sheng00125/LIV_handhold/livox_ros_driver/livox_ros_driver/livox_ros_driver.cpp

//
// The MIT License (MIT)
//
// Copyright (c) 2019 Livox. All rights reserved.
//
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

#include "include/livox_ros_driver.h"

#include <chrono>
#include <vector>
#include <csignal>

#include <ros/ros.h>
#include "lddc.h"
#include "lds_hub.h"
#include "lds_lidar.h"
#include "lds_lvx.h"
#include "livox_sdk.h"
#include <sys/stat.h>
#include <unistd.h>
using namespace livox_ros;

const int32_t kSdkVersionMajorLimit = 2;

inline void SignalHandler(int signum) {
  printf("livox ros driver will exit\r\n");
  ros::shutdown();
  exit(signum);
}

struct time_stamp {
  int64_t high;
  int64_t low;
};
struct time_stamp *pointt;
#define ERR_EXIT(m)                                                            \
  do {                                                                         \
    perror(m);                                                                 \
    exit(EXIT_FAILURE);                                                        \
  } while (0)

int main(int argc, char **argv) {
  /** Ros related */
  if (ros::console::set_logger_level(ROSCONSOLE_DEFAULT_NAME,
                                     ros::console::levels::Debug)) {
    ros::console::notifyLoggerLevelsChanged();
  }
  ros::init(argc, argv, "livox_lidar_publisher");
  ros::NodeHandle livox_node;

  ROS_INFO("Livox Ros Driver Version: %s", LIVOX_ROS_DRIVER_VERSION_STRING);
  signal(SIGINT, SignalHandler);
  /** Check sdk version */
  LivoxSdkVersion _sdkversion;
  GetLivoxSdkVersion(&_sdkversion);
  if (_sdkversion.major < kSdkVersionMajorLimit) {
    ROS_INFO("The SDK version[%d.%d.%d] is too low", _sdkversion.major,
             _sdkversion.minor, _sdkversion.patch);
    return 0;
  }

  /** Init default system parameter */
  int xfer_format = kPointCloud2Msg;
  int multi_topic = 0;
  int data_src = kSourceRawLidar;
  double publish_freq  = 10.0; /* Hz */
  int output_type      = kOutputToRos;
  std::string frame_id = "livox_frame";
  bool lidar_bag = true;
  bool imu_bag   = false;
  livox_node.getParam("xfer_format", xfer_format);
  livox_node.getParam("multi_topic", multi_topic);
  livox_node.getParam("data_src", data_src);
  livox_node.getParam("publish_freq", publish_freq);
  livox_node.getParam("output_data_type", output_type);
  livox_node.getParam("frame_id", frame_id);
  livox_node.getParam("enable_lidar_bag", lidar_bag);
  livox_node.getParam("enable_imu_bag", imu_bag);
  const char *user_name = getlogin();
  std::string path_for_time_stamp = "/home/" + std::string(user_name) + "/timeshare";
  const char *shared_file_name = path_for_time_stamp.c_str();
  int fd = open(shared_file_name, O_CREAT | O_RDWR | O_TRUNC, 0666);
  if (fd == -1) {
    ERR_EXIT("open");
  } else {
    printf("open code: %d\n", fd);
  }
  lseek(fd, sizeof(time_stamp) * 1, SEEK_SET);
  write(fd, "", 1);
  pointt = (time_stamp *)mmap(NULL, sizeof(time_stamp) * 1,
                              PROT_READ | PROT_WRITE, MAP_SHARED, fd, 0);

  if (publish_freq > 100.0) {
    publish_freq = 100.0;
  } else if (publish_freq < 0.1) {
    publish_freq = 0.1;
  } else {
    publish_freq = publish_freq;
  }

  /** Lidar data distribute control and lidar data source set */
  Lddc *lddc = new Lddc(xfer_format, multi_topic, data_src, output_type,
                        publish_freq, frame_id, lidar_bag, imu_bag);
  lddc->SetRosNode(&livox_node);

  int ret = 0;
  if (data_src == kSourceRawLidar) {
    ROS_INFO("Data Source is raw lidar.");

    std::string user_config_path;
    livox_node.getParam("user_config_path", user_config_path);
    ROS_INFO("Config file : %s", user_config_path.c_str());

    std::string cmdline_bd_code;
    livox_node.getParam("cmdline_str", cmdline_bd_code);

    std::vector<std::string> bd_code_list;
    ParseCommandlineInputBdCode(cmdline_bd_code.c_str(), bd_code_list);

    LdsLidar *read_lidar = LdsLidar::GetInstance(1000 / publish_freq);
    lddc->RegisterLds(static_cast<Lds *>(read_lidar));
    // 里面有回调函数
    ret = read_lidar->InitLdsLidar(bd_code_list, user_config_path.c_str());
    if (!ret) {
      ROS_INFO("Init lds lidar success!");
    } else {
      ROS_ERROR("Init lds lidar fail!");
    }
  } else if (data_src == kSourceRawHub) {
    ROS_INFO("Data Source is hub.");

    std::string user_config_path;
    livox_node.getParam("user_config_path", user_config_path);
    ROS_INFO("Config file : %s", user_config_path.c_str());

    std::string cmdline_bd_code;
    livox_node.getParam("cmdline_str", cmdline_bd_code);

    std::vector<std::string> bd_code_list;
    ParseCommandlineInputBdCode(cmdline_bd_code.c_str(), bd_code_list);

    LdsHub *read_hub = LdsHub::GetInstance(1000 / publish_freq);
    lddc->RegisterLds(static_cast<Lds *>(read_hub));
    ret = read_hub->InitLdsHub(bd_code_list, user_config_path.c_str());
    if (!ret) {
      ROS_INFO("Init lds hub success!");
    } else {
      ROS_ERROR("Init lds hub fail!");
    }
  } else {
    ROS_INFO("Data Source is lvx file.");

    std::string cmdline_file_path;
    livox_node.getParam("cmdline_file_path", cmdline_file_path);

    do {
      if (!IsFilePathValid(cmdline_file_path.c_str())) {
        ROS_ERROR("File path invalid : %s !", cmdline_file_path.c_str());
        break;
      }

      std::string rosbag_file_path;
      int path_end_pos = cmdline_file_path.find_last_of('.');
      rosbag_file_path = cmdline_file_path.substr(0, path_end_pos);
      rosbag_file_path += ".bag";

      LdsLvx *read_lvx = LdsLvx::GetInstance(1000 / publish_freq);
      lddc->RegisterLds(static_cast<Lds *>(read_lvx));
      lddc->CreateBagFile(rosbag_file_path);
      int ret = read_lvx->InitLdsLvx(cmdline_file_path.c_str());
      if (!ret) {
        ROS_INFO("Init lds lvx file success!");
      } else {
        ROS_ERROR("Init lds lvx file fail!");
      }
    } while (0);
  }

  ros::Time::init();
  while (ros::ok()) {
    lddc->DistributeLidarData();
  }
  munmap(pointt, sizeof(time_stamp) * 5);
  return 0;
}
