sheng00125/LIV_handhold/stm32_timersync-open/HARDWARE/TIMER/timer.c

#include "timer.h"
#include "led.h"
#include "usart.h"
#include "sys.h"
#include <stdio.h>
#include <string.h>

//1,增加TIM3_PWM_Init函数。
//2,增加LED0_PWM_VAL宏定义，控制TIM3_CH2脉宽									  
//////////////////////////////////////////////////////////////////////////////////  
   	  
//通用定时器3中断初始化
//这里时钟选择为APB1的2倍，而APB1为36M
//arr：自动重装值。
//psc：时钟预分频数
//这里使用的是定时器3!
void TIM3_Int_Init(u16 arr,u16 psc)
{
  TIM_TimeBaseInitTypeDef  TIM_TimeBaseStructure;
	NVIC_InitTypeDef NVIC_InitStructure;

	RCC_APB1PeriphClockCmd(RCC_APB1Periph_TIM3, ENABLE); //时钟使能

	TIM_TimeBaseStructure.TIM_Period = arr; //设置在下一个更新事件装入活动的自动重装载寄存器周期的值	 计数到5000为500ms
	TIM_TimeBaseStructure.TIM_Prescaler =psc; //设置用来作为TIMx时钟频率除数的预分频值  10Khz的计数频率  
	TIM_TimeBaseStructure.TIM_ClockDivision = 0; //设置时钟分割:TDTS = Tck_tim
	TIM_TimeBaseStructure.TIM_CounterMode = TIM_CounterMode_Up;  //TIM向上计数模式
	TIM_TimeBaseInit(TIM3, &TIM_TimeBaseStructure); //根据TIM_TimeBaseInitStruct中指定的参数初始化TIMx的时间基数单位
 
	TIM_ITConfig(TIM3,TIM_IT_Update,ENABLE ); //使能指定的TIM3中断,允许更新中断

	NVIC_InitStructure.NVIC_IRQChannel = TIM3_IRQn;  //TIM3中断
	NVIC_InitStructure.NVIC_IRQChannelPreemptionPriority = 0;  //先占优先级0级
	NVIC_InitStructure.NVIC_IRQChannelSubPriority = 3;  //从优先级3级
	NVIC_InitStructure.NVIC_IRQChannelCmd = ENABLE; //IRQ通道被使能
	NVIC_Init(&NVIC_InitStructure);  //根据NVIC_InitStruct中指定的参数初始化外设NVIC寄存器

	TIM_Cmd(TIM3, ENABLE);  //使能TIMx外设
							 
}




vu16 varl=0;
//定时器3中断服务程序
vu16 var_Exp=0;
vu16 global_time;
char snum[7];
vu16 shorttt=0;

char gprmcStr[7]="$GPRMC,";
int chckNum=0;
char chckNumChar[2];

int ss=0;
int mm=0;
int hh=0;

unsigned char result;
int i;
int checkNum(const char *gprmcContext)
{
    if (gprmcContext == NULL) 
    {
        // printf("Input is NULL.\n");
        return -1;
		}

    result = gprmcContext[1];

    for (i = 2; gprmcContext[i] != '*' && gprmcContext[i] != '\0'; i++)
    {
        // printf("Processing character: %c (ASCII: %d)\n", gprmcContext[i], gprmcContext[i]);
        result ^= gprmcContext[i];
    }

    if (gprmcContext[i] != '*') 
    {
        // printf("No '*' found in the string.\n");
        return -1;
    }

    //printf("Final result before returning: %02X\n", result);
    return result;
}

char value_1[100]="";
char value_2[100]="";
char value_time[10]="";

char test[100]="$GPRMC,004015,A,2812.0498,N,11313.1361,E,0.0,180.0,150122,3.9,W,A*";
void TIM3_IRQHandler(void)   //TIM3中断
{


		if (TIM_GetITStatus(TIM3, TIM_IT_Update) != RESET) //检查指定的TIM中断发生与否:TIM 中断源 
		{
		TIM_ClearITPendingBit(TIM3, TIM_IT_Update  );  //清除TIMx的中断待处理位:TIM 中断源 
		LED1=!LED1;
			
			//var_Exp 做半曝光时长的相移操作
		TIM2->CNT=TIM2->ARR/2;

		PCout(13)=0;
		}
		
		
		//global_time++;
		//shorttt=0;
		//sprintf(snum, "%06d", global_time); //产生："000011D7"
		//snum[6]=0;
		//printf("$GPRMC,");
	  //printf(snum);
		//printf(".00,A,2237.496474,N,11356.089515,E,0.0,225.5,310518,2.3,W,A*23\n");
		

		
		//************************************* add *********************************************
		//UTCtime format: hhmmss
		
    if(ss<59){
				ss++;
		}else{
			  ss=0;
			 if(mm<59){
				 mm++;
			 }else{
				 mm=0;
				 if(hh<23){
					 hh++;
				 }else{
					 hh=0;
				 }
			 }
		}
		
    sprintf(value_2, "%s%02d%02d%02d%s", gprmcStr, hh, mm, ss, ".00,A,2237.496474,N,11356.089515,E,0.0,225.5,230520,2.3,W,A*");
		strcpy(value_1,value_2);
	  chckNum =checkNum(value_1);
	  sprintf(chckNumChar, "%02X", chckNum);
		printf("%s", value_2);
    printf("%s\n", chckNumChar);
	 
		
	  //**********************************************************************************

		/**
		chckNum=checkNum(test);	
	  sprintf(chckNumChar, "%02X", chckNum);
    printf("%s\n", chckNumChar);
    */
}



void TIM2_PWM_Init(u16 arr,u16 psc)
{  
	GPIO_InitTypeDef GPIO_InitStructure;
  TIM_TimeBaseInitTypeDef TIM_TimeBaseStructure;
  TIM_OCInitTypeDef TIM_OCInitStructure;
	

	RCC_APB1PeriphClockCmd(RCC_APB1Periph_TIM2, ENABLE); 
  RCC_APB2PeriphClockCmd(RCC_APB2Periph_GPIOA, ENABLE); 
	TIM_DeInit(TIM2);
 
 
	GPIO_InitStructure.GPIO_Pin = GPIO_Pin_1; //TIM_CH1  B6 pin out
	GPIO_InitStructure.GPIO_Mode = GPIO_Mode_AF_PP;  //??????
	GPIO_InitStructure.GPIO_Speed = GPIO_Speed_50MHz;
	GPIO_Init(GPIOA, &GPIO_InitStructure);//???GPIO
 
   //???TIM4
	TIM_TimeBaseStructure.TIM_Period = arr; 
	TIM_TimeBaseStructure.TIM_Prescaler =psc; 
	TIM_TimeBaseStructure.TIM_ClockDivision = 0; 
	TIM_TimeBaseStructure.TIM_CounterMode = TIM_CounterMode_Up;  
	TIM_TimeBaseInit(TIM2, &TIM_TimeBaseStructure); 
	
	//???TIM4 Channel1 PWM??	 
	TIM_OCInitStructure.TIM_Pulse = 50; //????????????????
	TIM_OCInitStructure.TIM_OCMode = TIM_OCMode_PWM2; //???????:TIM????????2
 	TIM_OCInitStructure.TIM_OutputState = TIM_OutputState_Enable; //??????
	TIM_OCInitStructure.TIM_OCPolarity = TIM_OCPolarity_High; //????:TIM???????
	TIM_OCInitStructure.TIM_OutputNState = TIM_OutputNState_Disable;
	TIM_OC2PreloadConfig(TIM2, TIM_OCPreload_Enable);  //??TIM4?CCR2????????
	TIM_OC2Init(TIM2, &TIM_OCInitStructure);  //??T??????????TIM4 OC2
	
	//???TIM4 Channel2 PWM??	 
//	TIM_OCInitStructure.TIM_Pulse = 500; //????????????????
//	TIM_OCInitStructure.TIM_OCMode = TIM_OCMode_PWM2; //???????:TIM????????2
// 	TIM_OCInitStructure.TIM_OutputState = TIM_OutputState_Enable; //??????
//	TIM_OCInitStructure.TIM_OCPolarity = TIM_OCPolarity_High; //????:TIM???????
//	//TIM_OCInitStructure.TIM_OutputNState = TIM_OutputNState_Disable;
//	TIM_OC2PreloadConfig(TIM4, TIM_OCPreload_Enable);  //??TIM4?CCR2????????
//	TIM_OC2Init(TIM4, &TIM_OCInitStructure);  //??T??????????TIM4 OC2

 	TIM_ARRPreloadConfig(TIM2, ENABLE);
	TIM_Cmd(TIM2, ENABLE);  //??TIM4
	


 //	TIM_SetCompare2(TIM2,50);	 // ccr  set pwm value
TIM_SetCompare2(TIM2,TIM2->ARR/2);
}



//TIM3 PWM部分初始化 
//PWM输出初始化
//arr：自动重装值
//psc：时钟预分频数

//
void TIM3_PWM_Init(u16 arr,u16 psc)
{  
	GPIO_InitTypeDef GPIO_InitStructure;
	TIM_TimeBaseInitTypeDef  TIM_TimeBaseStructure;
	TIM_OCInitTypeDef  TIM_OCInitStructure;
		NVIC_InitTypeDef NVIC_InitStructure;	

	RCC_APB1PeriphClockCmd(RCC_APB1Periph_TIM3, ENABLE);	//使能定时器3时钟
 	RCC_APB2PeriphClockCmd(RCC_APB2Periph_GPIOB  | RCC_APB2Periph_AFIO, ENABLE);  //使能GPIO外设和AFIO复用功能模块时钟
	
	GPIO_PinRemapConfig(GPIO_PartialRemap_TIM3, ENABLE); //Timer3部分重映射  TIM3_CH2->PB5    
 
   //设置该引脚为复用输出功能,输出TIM3 CH2的PWM脉冲波形	GPIOB.5
	GPIO_InitStructure.GPIO_Pin = GPIO_Pin_5; //TIM_CH2
	GPIO_InitStructure.GPIO_Mode = GPIO_Mode_AF_PP;  //复用推挽输出
	GPIO_InitStructure.GPIO_Speed = GPIO_Speed_50MHz;
	GPIO_Init(GPIOB, &GPIO_InitStructure);//初始化GPIO
 
   //初始化TIM3
	TIM_TimeBaseStructure.TIM_Period = arr; //设置在下一个更新事件装入活动的自动重装载寄存器周期的值
	TIM_TimeBaseStructure.TIM_Prescaler =psc; //设置用来作为TIMx时钟频率除数的预分频值 
	TIM_TimeBaseStructure.TIM_ClockDivision = 0; //设置时钟分割:TDTS = Tck_tim
	TIM_TimeBaseStructure.TIM_CounterMode = TIM_CounterMode_Up;  //TIM向上计数模式
	TIM_TimeBaseInit(TIM3, &TIM_TimeBaseStructure); //根据TIM_TimeBaseInitStruct中指定的参数初始化TIMx的时间基数单位
	
	//初始化TIM3 Channel2 PWM模式	 
	TIM_OCInitStructure.TIM_OCMode = TIM_OCMode_PWM2; //选择定时器模式:TIM脉冲宽度调制模式2
 	TIM_OCInitStructure.TIM_OutputState = TIM_OutputState_Enable; //比较输出使能
	TIM_OCInitStructure.TIM_OCPolarity = TIM_OCPolarity_High; //输出极性:TIM输出比较极性高
	TIM_OC2Init(TIM3, &TIM_OCInitStructure);  //根据T指定的参数初始化外设TIM3 OC2

	TIM_OC2PreloadConfig(TIM3, TIM_OCPreload_Enable);  //使能TIM3在CCR2上的预装载寄存器
 
	TIM_Cmd(TIM3, ENABLE);  //使能TIM3
	
	TIM_SetCompare2(TIM3,TIM3->ARR/2);	

	TIM_ITConfig(TIM3,TIM_IT_Update,ENABLE ); //使能指定的TIM3中断,允许更新中断

	NVIC_InitStructure.NVIC_IRQChannel = TIM3_IRQn;  //TIM3中断
	NVIC_InitStructure.NVIC_IRQChannelPreemptionPriority = 0;  //先占优先级0级
	NVIC_InitStructure.NVIC_IRQChannelSubPriority = 3;  //从优先级3级
	NVIC_InitStructure.NVIC_IRQChannelCmd = ENABLE; //IRQ通道被使能
	NVIC_Init(&NVIC_InitStructure);  //根据NVIC_InitStruct中指定的参数初始化外设NVIC寄存器
}
