sheng00125/LIV_handhold/livox_ros_driver/timesync/timesync.cpp

//
// The MIT License (MIT)
//
// Copyright (c) 2019 Livox. All rights reserved.
//
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

#include "timesync.h"

#include <stdint.h>
#include <string.h>
#include <chrono>
#include <cstdio>
#include <functional>
#include <thread>
#include <stdio.h>
namespace livox_ros {
using namespace std;

TimeSync::TimeSync()
    : exit_poll_state_(false),
      start_poll_state_(false),
      exit_poll_data_(false),
      start_poll_data_(false) {
  fsm_state_ = kOpenDev;
  uart_ = nullptr;
  comm_ = nullptr;
  fn_cb_ = nullptr;
  client_data_ = nullptr;
  rx_bytes_ = 0;
}

TimeSync::~TimeSync() { DeInitTimeSync(); }

int32_t TimeSync::InitTimeSync(const TimeSyncConfig &config) {
  config_ = config;

  if (config_.dev_config.type == kCommDevUart) {
    uint8_t baudrate_index = config_.dev_config.config.uart.baudrate;
    uint8_t parity_index = config_.dev_config.config.uart.parity;

    if ((baudrate_index < BRUnkown) && (parity_index < ParityUnkown)) {
      uart_ = new UserUart(baudrate_index, parity_index);
    } else {
      printf("Uart parameter error, please check the configuration file!\n");
      return -1;
    }
  } else {
    printf("Device type not supported, now only uart is supported!\n");
    return -1;
  }

  config_.protocol_config.type = kGps;
  comm_ = new CommProtocol(config_.protocol_config);

  t_poll_state_ =
      std::make_shared<std::thread>(std::bind(&TimeSync::PollStateLoop, this));
  t_poll_data_ =
      std::make_shared<std::thread>(std::bind(&TimeSync::PollDataLoop, this));

  return 0;
}

int32_t TimeSync::DeInitTimeSync() {
  StopTimesync();

  if (uart_) delete uart_;
  if (comm_) delete comm_;

  fn_cb_ = nullptr;
  client_data_ = nullptr;
  return 0;
}

void TimeSync::StopTimesync() {
  start_poll_state_ = false;
  start_poll_data_ = false;
  exit_poll_state_ = true;
  exit_poll_data_ = true;
  if (t_poll_state_) {
    t_poll_state_->join();
    t_poll_state_ = nullptr;
  }

  if (t_poll_data_) {
    t_poll_data_->join();
    t_poll_data_ = nullptr;
  }
}

void TimeSync::PollStateLoop() {
  while (!start_poll_state_) {
    /* waiting to start */
  }

  while (!exit_poll_state_) {
    if (fsm_state_ == kOpenDev) {
      FsmOpenDev();
    } else if (fsm_state_ == kPrepareDev) {
      FsmPrepareDev();
    } else if (fsm_state_ == kCheckDevState) {
      FsmCheckDevState();
    }
    std::this_thread::sleep_for(std::chrono::milliseconds(50));
  }
}

void TimeSync::PollDataLoop() {
  while (!start_poll_data_) {
    /* waiting to start */
  }

  while (!exit_poll_data_) {
    if (uart_->IsOpen()) {
      uint32_t get_buf_size;
      uint8_t *cache_buf = comm_->FetchCacheFreeSpace(&get_buf_size);
      if (get_buf_size) {
        uint32_t read_data_size;
        read_data_size = uart_->Read((char *)cache_buf, get_buf_size);
        if (read_data_size) {
          comm_->UpdateCacheWrIdx(read_data_size);
          rx_bytes_ += read_data_size;
          CommPacket packet;
          memset(&packet, 0, sizeof(packet));
          // 解析 $GPRMC
          while ((kParseSuccess == comm_->ParseCommStream(&packet))) {
            if (((fn_cb_ != nullptr) || (client_data_ != nullptr))) {
              if ((strstr((const char *)packet.data, "$GPRMC")) ||
                      (strstr((const char *)packet.data , "$GNRMC"))){
                // 这里把包的结果打印出来了
                printf("Received RMC data packet: %s\n", (const char *)packet.data);
                fn_cb_((const char *)packet.data,
                       packet.data_len, client_data_);
                // printf((const char *)client_data_);
                printf("RMC data parse success!.\n");
              }
            }
          }
        }
      }
    } else {
      std::this_thread::sleep_for(std::chrono::milliseconds(50));
    }
  }
}

void TimeSync::FsmTransferState(uint8_t new_state) {
  if (new_state < kFsmDevUndef) {
    fsm_state_ = new_state;
  }
  transfer_time_ = chrono::steady_clock::now();
}

void TimeSync::FsmOpenDev() {
  if (!uart_->IsOpen()) {
    if (!uart_->Open(config_.dev_config.name)) {
      FsmTransferState(kPrepareDev);
    }
  } else {
    FsmTransferState(kPrepareDev);
  }
}

void TimeSync::FsmPrepareDev() {
  chrono::steady_clock::time_point t = chrono::steady_clock::now();
  chrono::milliseconds time_gap =
      chrono::duration_cast<chrono::milliseconds>(t - transfer_time_);
  /** delay some time when device is opened, 4s */
  if (time_gap.count() > 3000) {
    FsmTransferState(kCheckDevState);
  }
}

void TimeSync::FsmCheckDevState() {
  static uint32_t last_rx_bytes = 0;
  static chrono::steady_clock::time_point t1 = chrono::steady_clock::now();

  chrono::steady_clock::time_point t2 = chrono::steady_clock::now();
  chrono::milliseconds time_gap =
      chrono::duration_cast<chrono::milliseconds>(t2 - t1);

  if (time_gap.count() > 2000000) { /* period : 2.5s */
    if (last_rx_bytes == rx_bytes_) {
      uart_->Close();
      FsmTransferState(kOpenDev);
      printf("Uart is disconnected, close it\n");
    }
    last_rx_bytes = rx_bytes_;
    t1 = t2;
  }
}

}  // namespace livox_ros
